mczerski/MySXMotion/img/IMG_20180707_143013.jpg

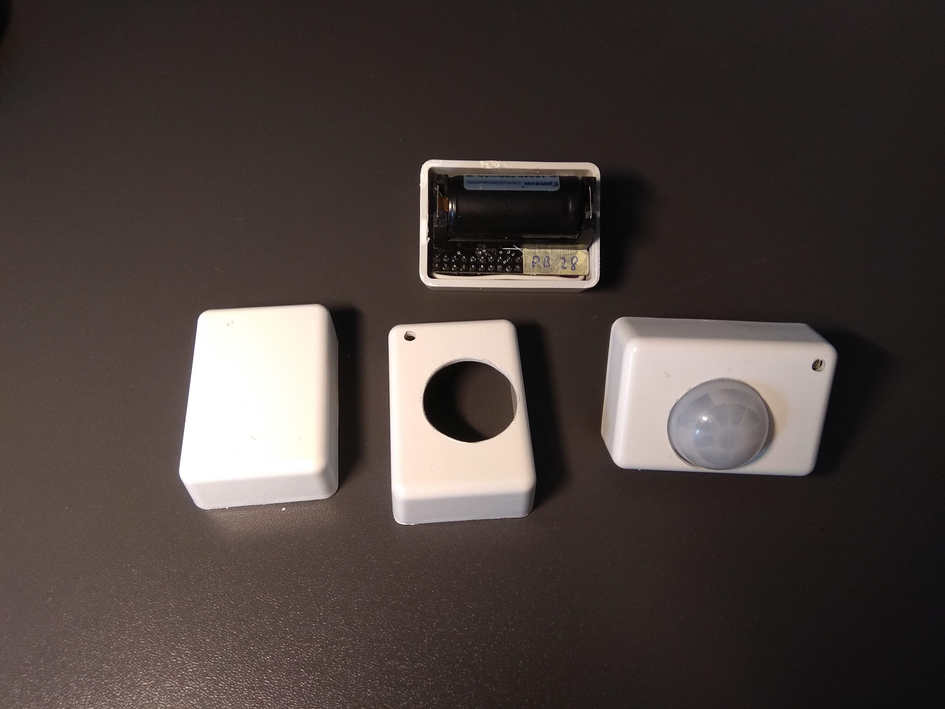
img/IMG_20180707_143013.jpg
