mczerski/MySXMotion/img/IMG_20180707_143056.jpg

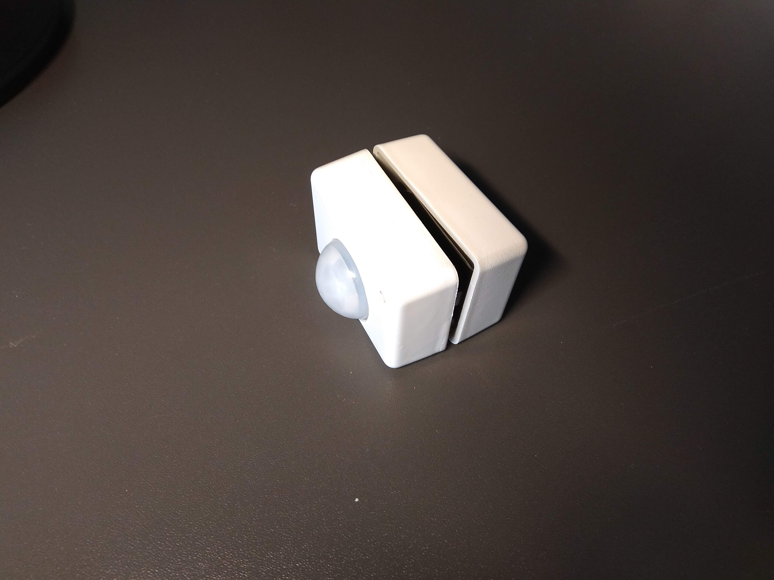
img/IMG_20180707_143056.jpg
