mczerski/MySXMotion/img/IMG_20180707_143127.jpg

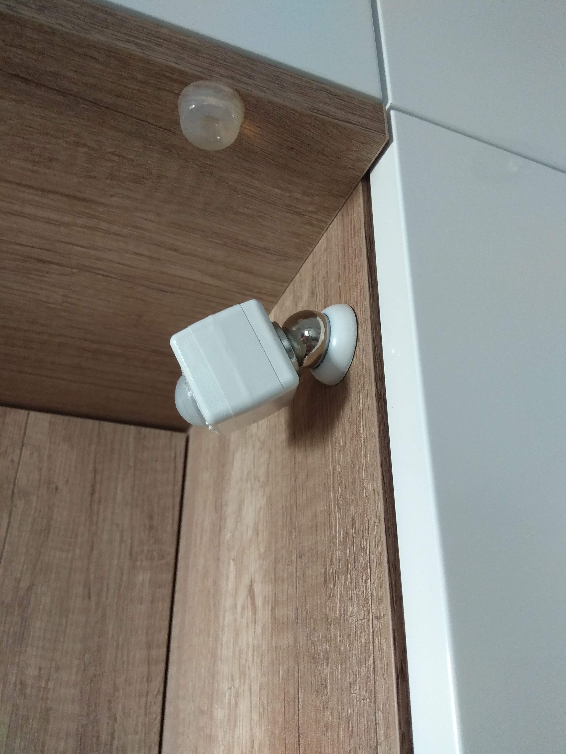
img/IMG_20180707_143127.jpg
